mczerski/MySMotherboard/img/IMG_20180708_110438.jpg

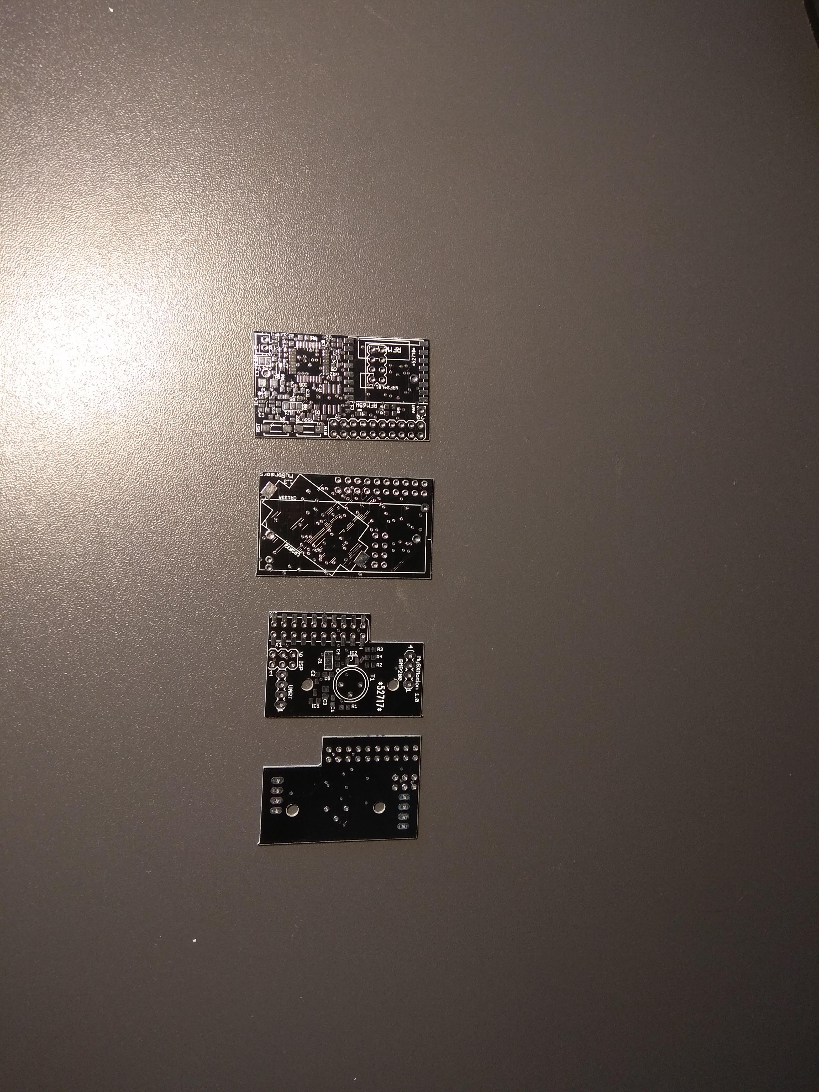
img/IMG_20180708_110438.jpg
